Vail-CW/vail-summit/src/settings/settings_cw.h

/*
 * CW Settings Module
 * Handles morse code speed, tone, and key type settings
 */

#ifndef SETTINGS_CW_H
#define SETTINGS_CW_H

#include <Preferences.h>
#include "../core/config.h"

// Key types
enum KeyType {
  KEY_STRAIGHT = 0,
  KEY_IAMBIC_A = 1,
  KEY_IAMBIC_B = 2,
  KEY_ULTIMATIC = 3
};

// CW settings state
enum CWSettingsState {
  CW_SETTING_SPEED,
  CW_SETTING_TONE,
  CW_SETTING_KEY_TYPE
};

// CW settings globals
CWSettingsState cwSettingState = CW_SETTING_SPEED;
int cwSpeed = DEFAULT_WPM;         // WPM
int cwTone = TONE_SIDETONE;        // Hz
KeyType cwKeyType = KEY_IAMBIC_B;  // Default to Iambic B
Preferences cwPrefs;

// Setting selection
int cwSettingSelection = 0;
#define CW_SETTINGS_COUNT 3

// LVGL mode flag - when true, skip legacy draw functions (LVGL handles display)
bool cwSettingsUseLVGL = true;  // Default to LVGL mode

// Forward declarations
void startCWSettings(LGFX &display);
void drawCWSettingsUI(LGFX &display);
int handleCWSettingsInput(char key, LGFX &display);
void saveCWSettings();
void loadCWSettings();

// Load CW settings from flash
void loadCWSettings() {
  if (!cwPrefs.begin("cw", true)) {
    // Namespace missing (fresh device) or NVS unhealthy - keep defaults
    Serial.println("[CW] WARNING: could not open 'cw' namespace read-only, using defaults");
  }
  cwSpeed = cwPrefs.getInt("speed", DEFAULT_WPM);
  cwTone = cwPrefs.getInt("tone", TONE_SIDETONE);
  cwKeyType = (KeyType)cwPrefs.getInt("keytype", KEY_IAMBIC_B);
  cwPrefs.end();

  // Validate settings
  if (cwSpeed < WPM_MIN) cwSpeed = WPM_MIN;
  if (cwSpeed > WPM_MAX) cwSpeed = WPM_MAX;
  if (cwTone < 400) cwTone = 400;
  if (cwTone > 1200) cwTone = 1200;

  Serial.print("CW Settings loaded: ");
  Serial.print(cwSpeed);
  Serial.print(" WPM, ");
  Serial.print(cwTone);
  Serial.print(" Hz, Key type: ");
  Serial.println(cwKeyType);
}

// Save CW settings to flash
void saveCWSettings() {
  if (!cwPrefs.begin("cw", false)) {
    Serial.println("[CW] ERROR: cannot open 'cw' namespace for write - settings NOT saved");
    return;
  }
  // putInt returns bytes written (0 = failure, e.g. NVS partition full)
  bool ok = true;
  ok &= cwPrefs.putInt("speed", cwSpeed) > 0;
  ok &= cwPrefs.putInt("tone", cwTone) > 0;
  ok &= cwPrefs.putInt("keytype", (int)cwKeyType) > 0;
  cwPrefs.end();

  if (ok) {
    Serial.println("CW Settings saved");
  } else {
    Serial.println("[CW] ERROR: NVS write failed (partition full or corrupt?) - settings NOT saved");
  }
}

// Start CW settings mode
void startCWSettings(LGFX &display) {
  cwSettingSelection = 0;
  drawCWSettingsUI(display);
}

// Draw CW settings UI
void drawCWSettingsUI(LGFX &display) {
  if (cwSettingsUseLVGL) return;  // LVGL handles display
  // Clear screen (preserve header)
  display.fillRect(0, HEADER_HEIGHT + 2, SCREEN_WIDTH, SCREEN_HEIGHT - HEADER_HEIGHT - 2, COLOR_BACKGROUND);

  // Clean container card
  int cardX = 20;
  int cardY = 60;
  int cardW = SCREEN_WIDTH - 40;
  int cardH = 150;

  // Solid card background
  display.fillRoundRect(cardX, cardY, cardW, cardH, 10, COLOR_BG_LAYER2);

  // Subtle border
  display.drawRoundRect(cardX, cardY, cardW, cardH, 10, COLOR_BORDER_SUBTLE);

  // Setting 0: Speed (WPM)
  int yPos = cardY + 15;
  bool isSelected = (cwSettingSelection == 0);

  if (isSelected) {
    // Clean selection highlight
    display.fillRoundRect(cardX + 8, yPos, cardW - 16, 36, 8, COLOR_CARD_CYAN);
    display.drawRoundRect(cardX + 8, yPos, cardW - 16, 36, 8, COLOR_BORDER_ACCENT);
  }

  display.setTextSize(1);
  display.setTextColor(isSelected ? COLOR_TEXT_PRIMARY : COLOR_TEXT_SECONDARY);
  display.setCursor(cardX + 15, yPos + 8);
  display.print("Speed");

  display.setTextSize(2);
  display.setTextColor(isSelected ? COLOR_ACCENT_CYAN : COLOR_TEXT_SECONDARY);
  display.setCursor(cardX + 15, yPos + 20);
  display.print(cwSpeed);
  display.print(" WPM");

  // Setting 1: Tone (Hz)
  yPos += 45;
  isSelected = (cwSettingSelection == 1);

  if (isSelected) {
    // Clean selection highlight
    display.fillRoundRect(cardX + 8, yPos, cardW - 16, 36, 8, COLOR_CARD_CYAN);
    display.drawRoundRect(cardX + 8, yPos, cardW - 16, 36, 8, COLOR_BORDER_ACCENT);
  }

  display.setTextSize(1);
  display.setTextColor(isSelected ? COLOR_TEXT_PRIMARY : COLOR_TEXT_SECONDARY);
  display.setCursor(cardX + 15, yPos + 8);
  display.print("Tone");

  display.setTextSize(2);
  display.setTextColor(isSelected ? COLOR_ACCENT_CYAN : COLOR_TEXT_SECONDARY);
  display.setCursor(cardX + 15, yPos + 20);
  display.print(cwTone);
  display.print(" Hz");

  // Setting 2: Key Type
  yPos += 45;
  isSelected = (cwSettingSelection == 2);

  if (isSelected) {
    // Clean selection highlight
    display.fillRoundRect(cardX + 8, yPos, cardW - 16, 36, 8, COLOR_CARD_CYAN);
    display.drawRoundRect(cardX + 8, yPos, cardW - 16, 36, 8, COLOR_BORDER_ACCENT);
  }

  display.setTextSize(1);
  display.setTextColor(isSelected ? COLOR_TEXT_PRIMARY : COLOR_TEXT_SECONDARY);
  display.setCursor(cardX + 15, yPos + 8);
  display.print("Key Type");

  display.setTextSize(2);
  display.setTextColor(isSelected ? COLOR_ACCENT_CYAN : COLOR_TEXT_SECONDARY);
  display.setCursor(cardX + 15, yPos + 20);
  if (cwKeyType == KEY_STRAIGHT) {
    display.print("Straight");
  } else if (cwKeyType == KEY_IAMBIC_A) {
    display.print("Iambic A");
  } else if (cwKeyType == KEY_IAMBIC_B) {
    display.print("Iambic B");
  } else {
    display.print("Ultimatic");
  }

  // Draw footer instructions
  display.setTextSize(1);
  display.setTextColor(COLOR_WARNING);
  String footerText = "\x18\x19 Select  \x1B\x1A Adjust  ESC Back";

  int16_t x1, y1;
  uint16_t w, h;
  getTextBounds_compat(display, footerText.c_str(), 0, 0, &x1, &y1, &w, &h);
  int centerX = (SCREEN_WIDTH - w) / 2;
  display.setCursor(centerX, SCREEN_HEIGHT - 12);
  display.print(footerText);
}

// Handle CW settings input
int handleCWSettingsInput(char key, LGFX &display) {
  bool changed = false;

  if (key == KEY_UP) {
    if (cwSettingSelection > 0) {
      cwSettingSelection--;
      beep(TONE_MENU_NAV, BEEP_SHORT);
      drawCWSettingsUI(display);
    }
    return 1;
  }
  else if (key == KEY_DOWN) {
    if (cwSettingSelection < CW_SETTINGS_COUNT - 1) {
      cwSettingSelection++;
      beep(TONE_MENU_NAV, BEEP_SHORT);
      drawCWSettingsUI(display);
    }
    return 1;
  }
  else if (key == KEY_LEFT) {
    // Decrease value
    if (cwSettingSelection == 0) {
      // Speed
      if (cwSpeed > WPM_MIN) {
        cwSpeed--;
        changed = true;
      }
    } else if (cwSettingSelection == 1) {
      // Tone
      if (cwTone > 400) {
        cwTone -= 50;
        changed = true;
      }
    } else if (cwSettingSelection == 2) {
      // Key type (cycle backward: Ultimatic -> Iambic B -> Iambic A -> Straight)
      if (cwKeyType == KEY_ULTIMATIC) {
        cwKeyType = KEY_IAMBIC_B;
        changed = true;
      } else if (cwKeyType == KEY_IAMBIC_B) {
        cwKeyType = KEY_IAMBIC_A;
        changed = true;
      } else if (cwKeyType == KEY_IAMBIC_A) {
        cwKeyType = KEY_STRAIGHT;
        changed = true;
      }
    }

    if (changed) {
      // Play tone preview if we're adjusting tone setting
      if (cwSettingSelection == 1) {
        beep(cwTone, 150);  // Play the new tone
      } else {
        beep(TONE_MENU_NAV, BEEP_SHORT);
      }
      saveCWSettings();
      drawCWSettingsUI(display);
    }
    return 1;
  }
  else if (key == KEY_RIGHT) {
    // Increase value
    if (cwSettingSelection == 0) {
      // Speed
      if (cwSpeed < WPM_MAX) {
        cwSpeed++;
        changed = true;
      }
    } else if (cwSettingSelection == 1) {
      // Tone
      if (cwTone < 1200) {
        cwTone += 50;
        changed = true;
      }
    } else if (cwSettingSelection == 2) {
      // Key type (cycle forward: Straight -> Iambic A -> Iambic B -> Ultimatic)
      if (cwKeyType == KEY_STRAIGHT) {
        cwKeyType = KEY_IAMBIC_A;
        changed = true;
      } else if (cwKeyType == KEY_IAMBIC_A) {
        cwKeyType = KEY_IAMBIC_B;
        changed = true;
      } else if (cwKeyType == KEY_IAMBIC_B) {
        cwKeyType = KEY_ULTIMATIC;
        changed = true;
      }
    }

    if (changed) {
      // Play tone preview if we're adjusting tone setting
      if (cwSettingSelection == 1) {
        beep(cwTone, 150);  // Play the new tone
      } else {
        beep(TONE_MENU_NAV, BEEP_SHORT);
      }
      saveCWSettings();
      drawCWSettingsUI(display);
    }
    return 1;
  }
  else if (key == KEY_ESC) {
    return -1;  // Exit CW settings
  }

  return 0;
}

#endif // SETTINGS_CW_H
