Vail-CW/vail-summit/src/training/training_practice.h

/*
 * Practice Oscillator Mode
 * Allows free-form morse code practice with paddle/key
 * Includes real-time morse decoding with adaptive speed tracking
 */

#ifndef TRAINING_PRACTICE_H
#define TRAINING_PRACTICE_H

#include "../core/config.h"
#include "../settings/settings_cw.h"
#include "../settings/settings_decoder.h"
#include "../audio/morse_decoder_adaptive.h"
#include "../audio/morse_decoder_direct.h"
#include "../audio/effective_wpm.h"
#include "../keyer/keyer.h"
#include <esp_timer.h>


// Practice mode state
bool practiceActive = false;
bool ditPressed = false;
bool dahPressed = false;
bool lastDitPressed = false;
bool lastDahPressed = false;
unsigned long practiceStartupTime = 0;  // Track startup time for input delay

// Deferred save state - debounces rapid setting changes when holding keys
unsigned long lastSettingSaveTime = 0;
bool settingSavePending = false;
#define SETTING_SAVE_DEBOUNCE_MS 500  // Save 500ms after last change

// Unified keyer instance
static StraightKeyer* practiceKeyer = nullptr;
int ditDuration = 0;

// Statistics
unsigned long practiceStartTime = 0;

// Decoder state - pointer selects Adaptive or Direct at runtime
static MorseDecoder* practiceDecoder = nullptr;

// Timer for direct decoder tick (only used when DECODER_DIRECT is active)
static esp_timer_handle_t decoderTickTimer = nullptr;
static volatile bool decoderTickPending = false;

static void decoderTickCallback(void*) {
  decoderTickPending = true;
}
String decodedText = "";
String decodedMorse = "";
bool showDecoding = true;
bool needsUIUpdate = false;

// Timing capture for decoder
unsigned long lastStateChangeTime = 0;
bool lastToneState = false;
unsigned long lastElementTime = 0;  // Track last element for timeout flush

// "Actual" (effective) WPM tracking - shared measurement (see effective_wpm.h),
// PARIS convention (5 chars = 1 word). Unlike the keyer speed setting, this
// reflects real throughput including any inter-character/word spacing the
// operator adds. Also used by Morse Notes recording so both readouts agree.
static EffectiveWpm practiceEffWpm;

// Forward declarations
void startPracticeMode(LGFX &display);
void updatePracticeOscillator();
void practiceKeyerCallback(bool txOn, int element);
float practiceGetActualWPM();

// LVGL-callable action functions
void practiceHandleEsc();
void practiceHandleClear();
void practiceAdjustSpeed(int delta);
void practiceCycleKeyType(int direction);
void practiceToggleDecoding();
void practiceCheckDeferredSave();

// Start practice mode
void startPracticeMode(LGFX &display) {
  practiceActive = true;
  ditPressed = false;
  dahPressed = false;
  practiceStartupTime = millis();  // Record startup time for input delay

  // Clear any lingering touch sensor state
  touchRead(TOUCH_DIT_PIN);
  touchRead(TOUCH_DAH_PIN);
  delay(50);

  // Reinitialize I2S to ensure clean state
  Serial.println("Reinitializing I2S for practice mode...");
  i2s_zero_dma_buffer(I2S_NUM_0);
  delay(50);

  // Calculate dit duration from current speed setting
  ditDuration = DIT_DURATION(cwSpeed);

  // Initialize unified keyer
  practiceKeyer = getKeyer(cwKeyType);
  practiceKeyer->reset();
  practiceKeyer->setDitDuration(ditDuration);
  practiceKeyer->setTxCallback(practiceKeyerCallback);

  // Reset statistics
  practiceStartTime = millis();

  // Stop any existing tick timer
  if (decoderTickTimer != nullptr) {
    esp_timer_stop(decoderTickTimer);
    esp_timer_delete(decoderTickTimer);
    decoderTickTimer = nullptr;
  }
  decoderTickPending = false;

  // Instantiate the selected decoder
  delete practiceDecoder;
  if (decoderType == DECODER_DIRECT) {
    practiceDecoder = new MorseDecoderDirect(cwSpeed, cwSpeed, 30);
    // Start 5ms periodic timer to drive direct decoder tick
    esp_timer_create_args_t timerArgs = {};
    timerArgs.callback = decoderTickCallback;
    timerArgs.name = "decoder_tick";
    esp_timer_create(&timerArgs, &decoderTickTimer);
    esp_timer_start_periodic(decoderTickTimer, 5000);  // 5000 µs = 5ms
  } else {
    practiceDecoder = new MorseDecoderAdaptive(cwSpeed, cwSpeed, 30);
  }
  practiceDecoder->reset();
  practiceDecoder->flush();
  practiceDecoder->setWPM(cwSpeed);
  decodedText = "";
  decodedMorse = "";
  lastStateChangeTime = 0;  // Don't initialize until first key press
  lastToneState = false;
  lastElementTime = 0;  // Reset element timeout tracker
  showDecoding = true;
  needsUIUpdate = false;
  practiceEffWpm.reset();

  // Setup decoder callbacks
  practiceDecoder->messageCallback = [](String morse, String text) {
    // Process each character in the decoded text individually
    for (int i = 0; i < text.length(); i++) {
      decodedText += text[i];
      // Feed the shared effective-WPM tracker (excludes word-space markers).
      // Counted here (not via decodedText.length()) because the display auto-
      // clears decodedText after 4 lines, which would otherwise reset the count.
      practiceEffWpm.onChar(text[i]);
    }

    // Also track morse pattern
    if (decodedMorse.length() + morse.length() > 100) {
      decodedMorse = "";  // Clear morse if it gets too long
    }
    decodedMorse += morse;

    needsUIUpdate = true;
    // No per-character Serial here: this runs in the keying path, and a
    // print into a full USB CDC buffer can stall the keyer.
  };

  practiceDecoder->speedCallback = [](float wpm, float fwpm) {
    // Fires on every element - no Serial (keying path, see above)
  };

  Serial.println("Practice mode started with decoding enabled");
  Serial.print("Speed: ");
  Serial.print(cwSpeed);
  Serial.print(" WPM, Tone: ");
  Serial.print(cwTone);
  Serial.print(" Hz, Key type: ");
  if (cwKeyType == KEY_STRAIGHT) {
    Serial.println("Straight");
  } else if (cwKeyType == KEY_IAMBIC_A) {
    Serial.println("Iambic A");
  } else if (cwKeyType == KEY_IAMBIC_B) {
    Serial.println("Iambic B");
  } else {
    Serial.println("Ultimatic");
  }
}


// Keyer callback - called by unified keyer when tone state changes
void practiceKeyerCallback(bool txOn, int element) {
  unsigned long currentTime = millis();

  if (txOn) {
    // Tone starting
    if (showDecoding && lastToneState == false) {
      // Send silence duration to decoder (negative). This may flush the
      // previous character (via addTiming's internal word-gap handling),
      // so the effective-WPM burst boundary below must be evaluated AFTER
      // this call, to credit that flushed char to the burst it belongs to.
      if (lastStateChangeTime > 0) {
        float silenceDuration = currentTime - lastStateChangeTime;
        if (silenceDuration > 0) {
          practiceDecoder->addTiming(-silenceDuration);
        }
      }
      lastStateChangeTime = currentTime;
      lastToneState = true;
    }
    practiceEffWpm.onToneStart(currentTime);
    startTone(cwTone);
  } else {
    // Tone stopping
    if (showDecoding && lastToneState == true) {
      // Send tone duration to decoder (positive)
      float toneDuration = currentTime - lastStateChangeTime;
      if (toneDuration > 0) {
        practiceDecoder->addTiming(toneDuration);
        lastElementTime = currentTime;  // Update timeout tracker
      }
      lastStateChangeTime = currentTime;
      lastToneState = false;
    }
    practiceEffWpm.onToneEnd(currentTime);
    stopTone();
  }
}

// Update practice oscillator (called in main loop)
void updatePracticeOscillator() {
  if (!practiceActive) return;
  if (!practiceKeyer) return;

  // Check for deferred settings save
  practiceCheckDeferredSave();

  // Ignore all input for first 1000ms to prevent startup glitches
  if (millis() - practiceStartupTime < 1000) {
    return;
  }

  // Service direct decoder tick (fires every 5ms via esp_timer)
  if (decoderTickPending) {
    decoderTickPending = false;
    if (showDecoding) practiceDecoder->tick();
  }

  // Flush buffered data after word gap silence
  if (showDecoding && lastElementTime > 0 && !ditPressed && !dahPressed) {
    unsigned long timeSinceLastElement = millis() - lastElementTime;
    float wordGapDuration = MorseWPM::wordGap(practiceDecoder->getWPM());
    if (timeSinceLastElement > wordGapDuration) {
      practiceDecoder->flush();
      lastElementTime = 0;
    }
  }

  // Get paddle state from centralized handler (includes debounce)
  bool newDitPressed, newDahPressed;
  getPaddleState(&newDitPressed, &newDahPressed);

  // Feed paddle state to unified keyer
  if (newDitPressed != ditPressed) {
    practiceKeyer->key(PADDLE_DIT, newDitPressed);
    ditPressed = newDitPressed;
  }
  if (newDahPressed != dahPressed) {
    practiceKeyer->key(PADDLE_DAH, newDahPressed);
    dahPressed = newDahPressed;
  }

  // Tick the keyer state machine
  practiceKeyer->tick(millis());

  // Keep tone playing if keyer is active (for audio buffer continuity)
  if (practiceKeyer->isTxActive()) {
    continueTone(cwTone);
  }

  // Update visual feedback if state changed
  if (ditPressed != lastDitPressed || dahPressed != lastDahPressed) {
    lastDitPressed = ditPressed;
    lastDahPressed = dahPressed;
  }
}

// ============================================
// LVGL-Callable Action Functions
// ============================================

// Handle ESC key - stop practice and prepare for exit
void practiceHandleEsc() {
  practiceActive = false;
  stopTone();
  if (decoderTickTimer != nullptr) {
    esp_timer_stop(decoderTickTimer);
    esp_timer_delete(decoderTickTimer);
    decoderTickTimer = nullptr;
  }
  decoderTickPending = false;
  if (practiceKeyer) {
    practiceKeyer->reset();
  }
  practiceDecoder->flush();  // Decode any remaining buffered timings
  practiceEffWpm.reset();

  // Save any pending settings before exit
  if (settingSavePending) {
    markDeferredSave(saveCWSettings);
    settingSavePending = false;
    Serial.println("[Practice] Saved pending settings on exit");
  }

  Serial.println("[Practice] ESC - exiting practice mode");
}

// Clear decoder text
void practiceHandleClear() {
  decodedText = "";
  decodedMorse = "";
  practiceDecoder->reset();
  practiceDecoder->flush();
  practiceEffWpm.reset();
  needsUIUpdate = true;  // Signal LVGL to update display
  beep(TONE_MENU_NAV, BEEP_SHORT);
  Serial.println("[Practice] Cleared decoder text");
}

// Adjust WPM speed (delta can be any value, e.g., 1, 2, 4 based on acceleration)
void practiceAdjustSpeed(int delta) {
  int newSpeed = cwSpeed + delta;
  if (newSpeed >= WPM_MIN && newSpeed <= WPM_MAX) {
    cwSpeed = newSpeed;
    ditDuration = DIT_DURATION(cwSpeed);
    practiceDecoder->setWPM(cwSpeed);
    if (practiceKeyer) {
      practiceKeyer->setDitDuration(ditDuration);
    }

    // Mark save as pending instead of immediate save (debounces rapid changes)
    settingSavePending = true;
    lastSettingSaveTime = millis();

    beep(TONE_MENU_NAV, BEEP_SHORT);
    Serial.printf("[Practice] Speed changed to %d WPM (save pending)\n", cwSpeed);
  }
}

// Check and perform deferred save of CW settings
// Call this from updatePracticeOscillator() to save after debounce period
void practiceCheckDeferredSave() {
  if (settingSavePending && (millis() - lastSettingSaveTime > SETTING_SAVE_DEBOUNCE_MS)) {
    markDeferredSave(saveCWSettings);
    settingSavePending = false;
    Serial.println("[Practice] Deferred CW settings save completed");
  }
}

// Cycle key type (+1 forward, -1 backward)
void practiceCycleKeyType(int direction) {
  if (direction > 0) {
    // Cycle forward: Straight -> Iambic A -> Iambic B -> Ultimatic -> Straight
    if (cwKeyType == KEY_STRAIGHT) {
      cwKeyType = KEY_IAMBIC_A;
    } else if (cwKeyType == KEY_IAMBIC_A) {
      cwKeyType = KEY_IAMBIC_B;
    } else if (cwKeyType == KEY_IAMBIC_B) {
      cwKeyType = KEY_ULTIMATIC;
    } else {
      cwKeyType = KEY_STRAIGHT;
    }
  } else {
    // Cycle backward: Ultimatic -> Iambic B -> Iambic A -> Straight -> Ultimatic
    if (cwKeyType == KEY_ULTIMATIC) {
      cwKeyType = KEY_IAMBIC_B;
    } else if (cwKeyType == KEY_IAMBIC_B) {
      cwKeyType = KEY_IAMBIC_A;
    } else if (cwKeyType == KEY_IAMBIC_A) {
      cwKeyType = KEY_STRAIGHT;
    } else {
      cwKeyType = KEY_ULTIMATIC;
    }
  }

  // Reinitialize keyer with new type
  practiceKeyer = getKeyer(cwKeyType);
  practiceKeyer->reset();
  practiceKeyer->setDitDuration(ditDuration);
  practiceKeyer->setTxCallback(practiceKeyerCallback);

  // Mark save as pending (use same debounce as speed changes)
  settingSavePending = true;
  lastSettingSaveTime = millis();

  beep(TONE_MENU_NAV, BEEP_SHORT);

  const char* keyTypeStr = (cwKeyType == KEY_STRAIGHT) ? "Straight" :
                           (cwKeyType == KEY_IAMBIC_A) ? "Iambic A" :
                           (cwKeyType == KEY_IAMBIC_B) ? "Iambic B" : "Ultimatic";
  Serial.printf("[Practice] Key type changed to %s (save pending)\n", keyTypeStr);
}

// Toggle decoding display
void practiceToggleDecoding() {
  showDecoding = !showDecoding;
  beep(TONE_MENU_NAV, BEEP_SHORT);
  Serial.printf("[Practice] Decoding %s\n", showDecoding ? "enabled" : "disabled");
}

// Get the current "actual" (effective) WPM reading for the CW Practice
// screen - the current sending burst only (responsive; freezes at its last
// value during a pause; -1 until there's a valid reading).
float practiceGetActualWPM() {
  return practiceEffWpm.burstWpm();
}

#endif // TRAINING_PRACTICE_H
