Vail-CW/vail-summit/src/core/task_manager.h

/*
 * VAIL SUMMIT - FreeRTOS Task Manager
 * Dual-core task management for ESP32-S3
 *
 * Core 0: Audio Task (high priority) - I2S generation, morse tones, decoder timing
 * Core 1: UI Task (Arduino loop) - LVGL rendering, input handling, network
 */

#ifndef TASK_MANAGER_H
#define TASK_MANAGER_H

#include <freertos/FreeRTOS.h>
#include <freertos/task.h>
#include <freertos/queue.h>
#include <freertos/semphr.h>
#include "config.h"
#include "morse_code.h"

// ============================================
// Task Configuration
// ============================================

#define AUDIO_TASK_STACK_SIZE   8192    // Stack size for audio task
#define AUDIO_TASK_PRIORITY     (configMAX_PRIORITIES - 1)  // Highest priority
// Run audio on Core 0. Core 1 (the Arduino/LVGL loop + display SPI-DMA) caused
// CONSTANT distortion - the audio task fights the display renderer continuously.
// Core 0 is clean in steady state; its only artifact is a brief (~10s) startup
// distortion while the WiFi stack (also Core 0) is connecting, which the larger
// I2S DMA buffer (see i2s_audio.h) is meant to ride out.
#define AUDIO_TASK_CORE         0

// ============================================
// Task Handles
// ============================================

static TaskHandle_t audioTaskHandle = NULL;

// ============================================
// Thread-Safe Audio Request Structure
// ============================================

// Tone request types
enum ToneRequestType {
    TONE_REQ_NONE = 0,
    TONE_REQ_PLAY,          // Play a tone for specific duration
    TONE_REQ_START,         // Start continuous tone
    TONE_REQ_CONTINUE,      // Continue current tone (fill buffer)
    TONE_REQ_STOP           // Stop current tone
};

// Thread-safe tone request (written by UI core, read by audio core)
struct ToneRequest {
    volatile ToneRequestType type;
    volatile int frequency;
    volatile int duration_ms;
};

static volatile ToneRequest toneRequest = {TONE_REQ_NONE, 0, 0};

// Audio state (managed by audio task, read by UI for status)
static volatile bool audioTaskRunning = false;
static volatile bool toneCurrentlyPlaying = false;
static volatile int currentToneFrequency = 0;

// Mutex for protecting shared state
static SemaphoreHandle_t audioMutex = NULL;

// ============================================
// Decoded Character Queue
// ============================================

// Queue for decoded characters (audio core produces, UI core consumes)
#define DECODED_CHAR_QUEUE_SIZE 32
static QueueHandle_t decodedCharQueue = NULL;

// ============================================
// Paddle Input State (sampled by audio task)
// ============================================

struct PaddleState {
    volatile bool ditPressed;
    volatile bool dahPressed;
    volatile unsigned long ditPressTime;
    volatile unsigned long dahPressTime;
    // Debounce state
    volatile bool ditRaw;
    volatile bool dahRaw;
    volatile unsigned long ditLastChange;
    volatile unsigned long dahLastChange;
};

static volatile PaddleState paddleState = {false, false, 0, 0, false, false, 0, 0};

// ============================================
// Core 0 Paddle Callback Support
// ============================================
// Allows modes to register a callback for paddle sampling on Core 0
// This provides precise ~1ms timing for keyer logic

// Paddle callback function type
// Called from Core 0 audio task with current paddle state and millis()
typedef void (*PaddleCallbackFn)(bool ditPressed, bool dahPressed, unsigned long now);

// Registered paddle callback (set by modes that need Core 0 timing)
static volatile PaddleCallbackFn paddleCallback = nullptr;

/*
 * Register a paddle callback to be called from Core 0
 * Set to nullptr to disable
 */
void registerPaddleCallback(PaddleCallbackFn callback) {
    paddleCallback = callback;
}

/*
 * Check if paddle callback is registered
 */
bool hasPaddleCallback() {
    return paddleCallback != nullptr;
}

// ============================================
// Async Morse String Playback
// ============================================

#define MORSE_PLAYBACK_MAX_LENGTH 128  // Max string length for async playback

// Morse playback state machine
enum MorsePlaybackState {
    MORSE_IDLE = 0,           // No playback active
    MORSE_PLAYING_ELEMENT,    // Playing a dit or dah
    MORSE_ELEMENT_GAP,        // Gap between dits/dahs in same letter
    MORSE_LETTER_GAP,         // Gap between letters
    MORSE_WORD_GAP,           // Gap between words
    MORSE_COMPLETE            // Playback finished
};

// Morse playback request structure
struct MorsePlaybackRequest {
    volatile bool active;           // Playback in progress
    volatile bool cancelled;        // Cancellation requested
    char text[MORSE_PLAYBACK_MAX_LENGTH];  // Text to play
    volatile int textLength;        // Length of text
    volatile int wpm;               // Words per minute (character speed)
    volatile int effectiveWPM;      // Effective WPM for Farnsworth (spacing speed)
    volatile bool useFarnsworth;    // Use Farnsworth timing (different element vs spacing speed)
    volatile int toneHz;            // Tone frequency
    volatile int charIndex;         // Current character in text
    volatile int elementIndex;      // Current element in character pattern
    volatile MorsePlaybackState state;  // Current state
    volatile unsigned long stateEndTime;  // When current state ends
    volatile bool complete;         // Playback finished flag
};

static volatile MorsePlaybackRequest morsePlayback = {
    false, false, "", 0, 0, 0, false, 0, 0, 0, MORSE_IDLE, 0, false
};

// Uses morseTable[] and getMorseCode() from morse_code.h (no duplicate table needed)

// ============================================
// Thread-Safe API Functions (called from UI core)
// ============================================

/*
 * Request a tone to be played
 * Non-blocking - sets request flags for audio task
 */
void requestPlayTone(int frequency, int duration_ms) {
    if (xSemaphoreTake(audioMutex, pdMS_TO_TICKS(10)) == pdTRUE) {
        toneRequest.frequency = frequency;
        toneRequest.duration_ms = duration_ms;
        toneRequest.type = TONE_REQ_PLAY;
        xSemaphoreGive(audioMutex);
    }
}

/*
 * Request to start a continuous tone
 */
void requestStartTone(int frequency) {
    if (xSemaphoreTake(audioMutex, pdMS_TO_TICKS(10)) == pdTRUE) {
        toneRequest.frequency = frequency;
        toneRequest.duration_ms = 0;
        toneRequest.type = TONE_REQ_START;
        xSemaphoreGive(audioMutex);
    }
}

/*
 * Request to stop the current tone
 */
void requestStopTone() {
    if (xSemaphoreTake(audioMutex, pdMS_TO_TICKS(10)) == pdTRUE) {
        toneRequest.type = TONE_REQ_STOP;
        xSemaphoreGive(audioMutex);
    }
}

/*
 * Request a beep (blocking on UI side - waits for completion)
 */
void requestBeep(int frequency, int duration_ms) {
    requestPlayTone(frequency, duration_ms);
    // Wait for tone to complete (approximate)
    vTaskDelay(pdMS_TO_TICKS(duration_ms + 20));
}

/*
 * Check if a tone is currently playing
 */
bool isAudioTonePlaying() {
    return toneCurrentlyPlaying;
}

/*
 * Get a decoded character from the queue (non-blocking)
 * Returns 0 if queue is empty
 */
char getDecodedChar() {
    char c = 0;
    if (decodedCharQueue != NULL) {
        xQueueReceive(decodedCharQueue, &c, 0);
    }
    return c;
}

/*
 * Check if there are decoded characters available
 */
bool hasDecodedChars() {
    if (decodedCharQueue == NULL) return false;
    return uxQueueMessagesWaiting(decodedCharQueue) > 0;
}

// ============================================
// Async Morse String Playback API (called from UI core)
// ============================================

/*
 * Request to play a morse string asynchronously
 * Non-blocking - returns immediately, audio task handles playback
 */
void requestPlayMorseString(const char* str, int wpm, int toneHz = TONE_SIDETONE) {
    if (str == nullptr || strlen(str) == 0) return;

    if (xSemaphoreTake(audioMutex, pdMS_TO_TICKS(20)) == pdTRUE) {
        // Stop any current playback
        morsePlayback.cancelled = true;

        // Wait a moment for audio task to see cancellation
        xSemaphoreGive(audioMutex);
        vTaskDelay(pdMS_TO_TICKS(10));

        // Now set up new playback
        if (xSemaphoreTake(audioMutex, pdMS_TO_TICKS(20)) == pdTRUE) {
            // Copy text (safely)
            int len = strlen(str);
            if (len > MORSE_PLAYBACK_MAX_LENGTH - 1) {
                len = MORSE_PLAYBACK_MAX_LENGTH - 1;
            }
            strncpy((char*)morsePlayback.text, str, len);
            ((char*)morsePlayback.text)[len] = '\0';

            morsePlayback.textLength = len;
            morsePlayback.wpm = wpm;
            morsePlayback.effectiveWPM = wpm;  // No Farnsworth - same as wpm
            morsePlayback.useFarnsworth = false;
            morsePlayback.toneHz = toneHz;
            morsePlayback.charIndex = 0;
            morsePlayback.elementIndex = 0;
            morsePlayback.state = MORSE_IDLE;  // Will start on next audio task cycle
            morsePlayback.stateEndTime = 0;
            morsePlayback.complete = false;
            morsePlayback.cancelled = false;
            morsePlayback.active = true;

            Serial.printf("[MorsePlayback] Started: '%s' @ %d WPM, %d Hz\n", str, wpm, toneHz);
            xSemaphoreGive(audioMutex);
        }
    }
}

/*
 * Request to play a morse string with Farnsworth timing asynchronously
 * characterWPM: speed for dits/dahs within a character (typically 25 WPM)
 * effectiveWPM: overall speed, determines inter-character/word spacing (typically 6-11 WPM)
 * Non-blocking - returns immediately, audio task handles playback
 */
void requestPlayMorseStringFarnsworth(const char* str, int characterWPM, int effectiveWPM, int toneHz = TONE_SIDETONE) {
    if (str == nullptr || strlen(str) == 0) return;

    if (xSemaphoreTake(audioMutex, pdMS_TO_TICKS(20)) == pdTRUE) {
        // Stop any current playback
        morsePlayback.cancelled = true;

        // Wait a moment for audio task to see cancellation
        xSemaphoreGive(audioMutex);
        vTaskDelay(pdMS_TO_TICKS(10));

        // Now set up new playback
        if (xSemaphoreTake(audioMutex, pdMS_TO_TICKS(20)) == pdTRUE) {
            // Copy text (safely)
            int len = strlen(str);
            if (len > MORSE_PLAYBACK_MAX_LENGTH - 1) {
                len = MORSE_PLAYBACK_MAX_LENGTH - 1;
            }
            strncpy((char*)morsePlayback.text, str, len);
            ((char*)morsePlayback.text)[len] = '\0';

            morsePlayback.textLength = len;
            morsePlayback.wpm = characterWPM;           // Character element speed
            morsePlayback.effectiveWPM = effectiveWPM;  // Spacing speed
            morsePlayback.useFarnsworth = (characterWPM != effectiveWPM);
            morsePlayback.toneHz = toneHz;
            morsePlayback.charIndex = 0;
            morsePlayback.elementIndex = 0;
            morsePlayback.state = MORSE_IDLE;  // Will start on next audio task cycle
            morsePlayback.stateEndTime = 0;
            morsePlayback.complete = false;
            morsePlayback.cancelled = false;
            morsePlayback.active = true;

            Serial.printf("[MorsePlayback] Farnsworth started: '%s' @ %d/%d WPM, %d Hz\n",
                          str, characterWPM, effectiveWPM, toneHz);
            xSemaphoreGive(audioMutex);
        }
    }
}

/*
 * Check if morse playback is currently active
 */
bool isMorsePlaybackActive() {
    return morsePlayback.active && !morsePlayback.complete;
}

/*
 * Check if morse playback has completed
 */
bool isMorsePlaybackComplete() {
    return morsePlayback.complete;
}

/*
 * Cancel current morse playback
 */
void cancelMorsePlayback() {
    if (xSemaphoreTake(audioMutex, pdMS_TO_TICKS(10)) == pdTRUE) {
        morsePlayback.cancelled = true;
        xSemaphoreGive(audioMutex);
    }
}

/*
 * Get current playback progress (0.0 to 1.0)
 */
float getMorsePlaybackProgress() {
    if (!morsePlayback.active || morsePlayback.textLength == 0) return 0.0f;
    return (float)morsePlayback.charIndex / (float)morsePlayback.textLength;
}

/*
 * Reset morse playback state (call when entering modes)
 */
void resetMorsePlayback() {
    if (xSemaphoreTake(audioMutex, pdMS_TO_TICKS(10)) == pdTRUE) {
        morsePlayback.active = false;
        morsePlayback.cancelled = false;
        morsePlayback.complete = false;
        morsePlayback.charIndex = 0;
        morsePlayback.elementIndex = 0;
        morsePlayback.state = MORSE_IDLE;
        xSemaphoreGive(audioMutex);
    }
}

// ============================================
// Internal Audio Task Functions
// ============================================

// Forward declarations for i2s_audio.h functions that will be called internally
extern void playToneInternal(int frequency, int duration_ms);
extern void IRAM_ATTR startToneInternal(int frequency);
extern void IRAM_ATTR continueToneInternal(int frequency);
extern void IRAM_ATTR stopToneInternal();
extern bool isTonePlayingInternal();

/*
 * Process audio requests from the queue
 * Called by audio task
 */
void IRAM_ATTR processAudioRequests() {
    ToneRequestType reqType = TONE_REQ_NONE;
    int reqFreq = 0;
    int reqDuration = 0;

    // Get current request with mutex protection
    if (xSemaphoreTake(audioMutex, pdMS_TO_TICKS(5)) == pdTRUE) {
        reqType = toneRequest.type;
        reqFreq = toneRequest.frequency;
        reqDuration = toneRequest.duration_ms;
        toneRequest.type = TONE_REQ_NONE;  // Clear request
        xSemaphoreGive(audioMutex);
    }

    // Process the request
    switch (reqType) {
        case TONE_REQ_PLAY:
            toneCurrentlyPlaying = true;
            currentToneFrequency = reqFreq;
            playToneInternal(reqFreq, reqDuration);
            toneCurrentlyPlaying = false;
            currentToneFrequency = 0;
            break;

        case TONE_REQ_START:
            toneCurrentlyPlaying = true;
            currentToneFrequency = reqFreq;
            startToneInternal(reqFreq);
            break;

        case TONE_REQ_CONTINUE:
            if (toneCurrentlyPlaying) {
                continueToneInternal(currentToneFrequency);
            }
            break;

        case TONE_REQ_STOP:
            stopToneInternal();
            toneCurrentlyPlaying = false;
            currentToneFrequency = 0;
            break;

        default:
            // If tone is playing, keep buffer filled
            if (toneCurrentlyPlaying) {
                continueToneInternal(currentToneFrequency);
            }
            break;
    }
}

/*
 * Sample paddle input and call registered callback
 * Called by audio task for precise timing (~1ms intervals)
 * Includes debounce to prevent double-dits from contact bounce
 */
void IRAM_ATTR samplePaddleInput() {
    // Read raw paddle pins
    bool rawDit = (digitalRead(DIT_PIN) == PADDLE_ACTIVE);
    bool rawDah = (digitalRead(DAH_PIN) == PADDLE_ACTIVE);

    // Read capacitive touch
    if (!rawDit) {
        rawDit = (touchRead(TOUCH_DIT_PIN) > TOUCH_THRESHOLD);
    }
    if (!rawDah) {
        rawDah = (touchRead(TOUCH_DAH_PIN) > TOUCH_THRESHOLD);
    }

    unsigned long now = millis();

    // Debounce dit paddle - only register change after stable for PADDLE_DEBOUNCE_MS
    if (rawDit != paddleState.ditRaw) {
        paddleState.ditLastChange = now;
        paddleState.ditRaw = rawDit;
    }
    bool dit = paddleState.ditPressed;
    if ((now - paddleState.ditLastChange) >= PADDLE_DEBOUNCE_MS) {
        dit = paddleState.ditRaw;
    }

    // Debounce dah paddle
    if (rawDah != paddleState.dahRaw) {
        paddleState.dahLastChange = now;
        paddleState.dahRaw = rawDah;
    }
    bool dah = paddleState.dahPressed;
    if ((now - paddleState.dahLastChange) >= PADDLE_DEBOUNCE_MS) {
        dah = paddleState.dahRaw;
    }

    // Update state with timestamps
    if (dit && !paddleState.ditPressed) {
        paddleState.ditPressTime = now;
    }
    if (dah && !paddleState.dahPressed) {
        paddleState.dahPressTime = now;
    }

    paddleState.ditPressed = dit;
    paddleState.dahPressed = dah;

    // Call registered paddle callback if set (for Core 0 keyer timing)
    if (paddleCallback != nullptr) {
        paddleCallback(dit, dah, now);
    }
}

/*
 * Get current paddle state (called from UI or decoder)
 */
void getPaddleState(bool* dit, bool* dah) {
    *dit = paddleState.ditPressed;
    *dah = paddleState.dahPressed;
}

/*
 * Process morse string playback state machine
 * Called by audio task - runs non-blocking state machine for async playback
 */
void IRAM_ATTR processMorsePlayback() {
    // Skip if no active playback
    if (!morsePlayback.active) return;

    // Check for cancellation
    if (morsePlayback.cancelled) {
        stopToneInternal();
        morsePlayback.active = false;
        morsePlayback.complete = true;
        morsePlayback.cancelled = false;
        // No Serial here - this runs on the IRAM audio hot path and
        // Serial.print* is flash-resident. (Was "[MorsePlayback] Cancelled".)
        return;
    }

    unsigned long now = millis();

    // Calculate timing based on WPM
    // Standard: 1 unit = 1200/WPM ms
    int charUnit = 1200 / morsePlayback.wpm;  // For dits/dahs within character
    int spaceUnit = charUnit;  // Default same as character

    // Farnsworth timing: use slower effective WPM for inter-character/word spacing
    if (morsePlayback.useFarnsworth && morsePlayback.effectiveWPM > 0) {
        spaceUnit = 1200 / morsePlayback.effectiveWPM;
    }

    int ditDuration = charUnit;
    int dahDuration = charUnit * 3;
    int elementGap = charUnit;       // Gap between elements within a character (always use char speed)
    int letterGap = spaceUnit * 3;   // Gap between characters (Farnsworth stretches this)
    int wordGap = spaceUnit * 7;     // Gap between words (Farnsworth stretches this)

    // State machine
    switch (morsePlayback.state) {
        case MORSE_IDLE: {
            // Start playing - find first valid character
            while (morsePlayback.charIndex < morsePlayback.textLength) {
                char c = morsePlayback.text[morsePlayback.charIndex];

                if (c == ' ') {
                    // Word gap - transition to MORSE_WORD_GAP
                    morsePlayback.state = MORSE_WORD_GAP;
                    morsePlayback.stateEndTime = now + (wordGap - letterGap);  // Subtract letter gap already added
                    morsePlayback.charIndex++;
                    return;
                }

                const char* pattern = getMorseCode(c);
                if (pattern != nullptr) {
                    // Valid character - start playing first element
                    morsePlayback.elementIndex = 0;
                    char element = pattern[0];

                    if (element == '.') {
                        startToneInternal(morsePlayback.toneHz);
                        morsePlayback.state = MORSE_PLAYING_ELEMENT;
                        morsePlayback.stateEndTime = now + ditDuration;
                    } else if (element == '-') {
                        startToneInternal(morsePlayback.toneHz);
                        morsePlayback.state = MORSE_PLAYING_ELEMENT;
                        morsePlayback.stateEndTime = now + dahDuration;
                    }
                    return;
                }

                // Unknown character - skip it
                morsePlayback.charIndex++;
            }

            // No more characters - playback complete
            morsePlayback.state = MORSE_COMPLETE;
            morsePlayback.complete = true;
            morsePlayback.active = false;
            // No Serial here - IRAM hot path. (Was "[MorsePlayback] Complete".)
            break;
        }

        case MORSE_PLAYING_ELEMENT: {
            // Keep I2S buffer filled during tone
            continueToneInternal(morsePlayback.toneHz);

            // Check if element duration has elapsed
            if (now >= morsePlayback.stateEndTime) {
                stopToneInternal();

                // Get current character pattern
                char c = morsePlayback.text[morsePlayback.charIndex];
                const char* pattern = getMorseCode(c);

                if (pattern == nullptr) {
                    // Should not happen, but handle gracefully
                    morsePlayback.charIndex++;
                    morsePlayback.state = MORSE_IDLE;
                    return;
                }

                // Move to next element
                morsePlayback.elementIndex++;

                if (pattern[morsePlayback.elementIndex] != '\0') {
                    // More elements in this character - add element gap
                    morsePlayback.state = MORSE_ELEMENT_GAP;
                    morsePlayback.stateEndTime = now + elementGap;
                } else {
                    // Character complete - move to next character
                    morsePlayback.charIndex++;

                    if (morsePlayback.charIndex >= morsePlayback.textLength) {
                        // All done
                        morsePlayback.state = MORSE_COMPLETE;
                        morsePlayback.complete = true;
                        morsePlayback.active = false;
                        // No Serial here - IRAM hot path. (Was "[MorsePlayback] Complete".)
                    } else if (morsePlayback.text[morsePlayback.charIndex] == ' ') {
                        // Next is space - word gap (already have letter gap implicitly)
                        morsePlayback.charIndex++;
                        morsePlayback.state = MORSE_WORD_GAP;
                        morsePlayback.stateEndTime = now + wordGap;
                    } else {
                        // Next is a character - letter gap
                        morsePlayback.state = MORSE_LETTER_GAP;
                        morsePlayback.stateEndTime = now + letterGap;
                    }
                }
            }
            break;
        }

        case MORSE_ELEMENT_GAP: {
            // Wait for element gap to complete
            if (now >= morsePlayback.stateEndTime) {
                // Start next element
                char c = morsePlayback.text[morsePlayback.charIndex];
                const char* pattern = getMorseCode(c);

                if (pattern != nullptr && pattern[morsePlayback.elementIndex] != '\0') {
                    char element = pattern[morsePlayback.elementIndex];

                    if (element == '.') {
                        startToneInternal(morsePlayback.toneHz);
                        morsePlayback.state = MORSE_PLAYING_ELEMENT;
                        morsePlayback.stateEndTime = now + ditDuration;
                    } else if (element == '-') {
                        startToneInternal(morsePlayback.toneHz);
                        morsePlayback.state = MORSE_PLAYING_ELEMENT;
                        morsePlayback.stateEndTime = now + dahDuration;
                    }
                } else {
                    // Pattern ended unexpectedly - move to next char
                    morsePlayback.charIndex++;
                    morsePlayback.state = MORSE_IDLE;
                }
            }
            break;
        }

        case MORSE_LETTER_GAP: {
            // Wait for letter gap to complete
            if (now >= morsePlayback.stateEndTime) {
                // Start next character
                morsePlayback.state = MORSE_IDLE;
            }
            break;
        }

        case MORSE_WORD_GAP: {
            // Wait for word gap to complete
            if (now >= morsePlayback.stateEndTime) {
                // Continue to next character
                morsePlayback.state = MORSE_IDLE;
            }
            break;
        }

        case MORSE_COMPLETE: {
            // Nothing to do - playback finished
            break;
        }
    }
}

// ============================================
// Audio Task
// ============================================

/*
 * Audio task - runs on Core 0
 * High priority, dedicated to audio processing
 */
void IRAM_ATTR audioTask(void* parameter) {
    Serial.println("[AudioTask] Started on Core 0");  // One-time, before the loop - fine.
    audioTaskRunning = true;

    while (true) {
#if AUDIO_PERF_INSTRUMENT
        uint32_t aperf_iter_start = micros();
#endif
        // Process any pending audio requests (single tone API)
        processAudioRequests();

        // Process morse string playback (async playback API)
        processMorsePlayback();

        // Sample paddle input with precise timing
        samplePaddleInput();

#if AUDIO_PERF_INSTRUMENT
        {
            uint32_t dt = micros() - aperf_iter_start;
            aperf_iterations++;
            if (dt > aperf_worst_loop_us) aperf_worst_loop_us = dt;
            if (dt > 5000) aperf_over5ms_count++;
        }
#endif

        // Yield to allow other tasks, but keep loop tight (~1ms)
        vTaskDelay(1);

        // Outside the measured region - this is the only place the once-per-
        // second Serial.printf report is allowed to run.
        reportAudioPerf();
    }
}

// ============================================
// Task Setup
// ============================================

/*
 * Initialize task manager and start audio task on Core 0
 * Call this from setup() after hardware initialization
 */
void setupTaskManager() {
    Serial.println("[TaskManager] Initializing...");

    // Create mutex for audio state protection
    audioMutex = xSemaphoreCreateMutex();
    if (audioMutex == NULL) {
        Serial.println("[TaskManager] ERROR: Failed to create audio mutex!");
        return;
    }

    // Create queue for decoded characters
    decodedCharQueue = xQueueCreate(DECODED_CHAR_QUEUE_SIZE, sizeof(char));
    if (decodedCharQueue == NULL) {
        Serial.println("[TaskManager] ERROR: Failed to create decoded char queue!");
        return;
    }

    // Create audio task pinned to Core 0
    BaseType_t result = xTaskCreatePinnedToCore(
        audioTask,              // Task function
        "AudioTask",            // Task name
        AUDIO_TASK_STACK_SIZE,  // Stack size
        NULL,                   // Parameters
        AUDIO_TASK_PRIORITY,    // Priority
        &audioTaskHandle,       // Task handle
        AUDIO_TASK_CORE         // Core ID
    );

    if (result != pdPASS) {
        Serial.println("[TaskManager] ERROR: Failed to create audio task!");
        return;
    }

    Serial.printf("[TaskManager] Audio task created on Core %d with priority %d\n",
                  AUDIO_TASK_CORE, AUDIO_TASK_PRIORITY);
    Serial.printf("[TaskManager] UI runs on Core %d (Arduino loop)\n", 1);
}

/*
 * Check if audio task is running
 */
bool isAudioTaskRunning() {
    return audioTaskRunning;
}

/*
 * Send a decoded character to the UI queue
 * Called from decoder running on audio task
 */
void sendDecodedChar(char c) {
    if (decodedCharQueue != NULL) {
        xQueueSend(decodedCharQueue, &c, 0);  // Non-blocking
    }
}

#endif // TASK_MANAGER_H
