Vail-CW/vail-summit/src/bluetooth/ble_midi.h

/*
 * BLE MIDI Mode
 * Bidirectional BLE MIDI for Vail repeater and MIDI-enabled morse tools
 * - Sends: Processed keyer output as MIDI Note On/Off
 * - Receives: Sidetone from computer, CC messages for speed/tone/keyer type
 *
 * MIDI Protocol (Vail Adapter Spec):
 * - Outgoing: Note 0 (C) for keyed output, Notes 1/2 for passthrough dit/dah
 * - Incoming CC1: Dit duration (speed), CC2: Sidetone note
 * - Incoming Program Change: Keyer type selection
 */

#ifndef BLE_MIDI_H
#define BLE_MIDI_H

#include <NimBLEDevice.h>
#include "ble_core.h"
#include "ble_keyboard_host.h"
#include "../core/config.h"
#include "../audio/i2s_audio.h"
#include "../settings/settings_cw.h"
#include "../keyer/keyer.h"

// BLE MIDI Service and Characteristic UUIDs (standard BLE MIDI spec)
#define MIDI_SERVICE_UUID        "03b80e5a-ede8-4b33-a751-6ce34ec4c700"
#define MIDI_CHARACTERISTIC_UUID "7772e5db-3868-4112-a1a9-f2669d106bf3"

// MIDI message types
#define MIDI_NOTE_OFF     0x80
#define MIDI_NOTE_ON      0x90
#define MIDI_CONTROL_CHANGE 0xB0
#define MIDI_PROGRAM_CHANGE 0xC0

// MIDI notes (Vail Adapter spec)
#define MIDI_NOTE_STRAIGHT 0   // C - Straight key / keyed output
#define MIDI_NOTE_DIT      1   // C# - Dit (passthrough mode)
#define MIDI_NOTE_DAH      2   // D - Dah (passthrough mode)

// MIDI Control Change numbers
#define MIDI_CC_DIT_DURATION 1  // CC1 - Dit duration in 2ms units
#define MIDI_CC_SIDETONE_NOTE 2 // CC2 - Sidetone MIDI note number

// MIDI Keyer Programs (Vail Adapter spec)
#define MIDI_KEYER_PASSTHROUGH  0
#define MIDI_KEYER_STRAIGHT     1
#define MIDI_KEYER_BUG          2
#define MIDI_KEYER_IAMBIC_A     7
#define MIDI_KEYER_IAMBIC_B     8

// BLE MIDI state
struct BLEMIDIState {
  bool active = false;
  bool isKeying = false;           // Current key state (for output)
  bool lastDitPressed = false;
  bool lastDahPressed = false;

  // MIDI-controlled settings
  int midiDitDuration = 0;         // 0 = use device settings
  int midiSidetoneNote = 69;       // A4 = 440Hz
  int midiKeyerProgram = MIDI_KEYER_IAMBIC_B;  // Default keyer type

  // BLE characteristics
  NimBLEService* midiService = nullptr;
  NimBLECharacteristic* midiCharacteristic = nullptr;

  unsigned long lastUpdateTime = 0;
};

BLEMIDIState btMIDI;

// Unified keyer for BT MIDI
static StraightKeyer* btMIDIKeyer = nullptr;
static bool btMIDIDitPressed = false;
static bool btMIDIDahPressed = false;

// Forward declarations
void startBTMIDI(LGFX& display);
void drawBTMIDIUI(LGFX& display);
int handleBTMIDIInput(char key, LGFX& display);
void updateBTMIDI();
void stopBTMIDI();
void sendMIDINoteOn(uint8_t note, uint8_t velocity);
void sendMIDINoteOff(uint8_t note);
void onMIDIReceived(uint8_t* data, size_t length);
void btMidiKeyerHandler();
void btMidiPassthroughHandler();
void btMidiInitKeyer();
int midiNoteToFrequency(int note);
int getDitDuration();
const char* getBTMIDIKeyerProgramName();

// Forward declarations for LVGL UI updates (defined in lv_mode_screens.h)
extern void updateBTMIDIStatus(const char* status, bool connected);
extern void updateBTMIDIDeviceName(const char* name);
extern void updateBTMIDIInfo(int wpm, bool fromMidi, const char* keyerName);
extern void updateBTMIDIKeyIndicator(bool keying);
extern void cleanupBTMIDIScreen();

// Track previous connection state for UI updates
static BLEConnectionState lastBTMIDIState = BLE_STATE_OFF;

const char* getBTMIDIKeyerProgramName() {
  switch (btMIDI.midiKeyerProgram) {
    case MIDI_KEYER_PASSTHROUGH: return "Passthrough";
    case MIDI_KEYER_STRAIGHT:    return "Straight";
    case MIDI_KEYER_BUG:         return "Bug";
    case MIDI_KEYER_IAMBIC_A:    return "Iambic A";
    case MIDI_KEYER_IAMBIC_B:    return "Iambic B";
    default:                     return "Unknown";
  }
}

// Push current speed + keyer program to the LVGL screen
static void refreshBTMIDIInfoDisplay() {
  int wpm = (btMIDI.midiDitDuration > 0) ? (1200 / btMIDI.midiDitDuration) : cwSpeed;
  updateBTMIDIInfo(wpm, btMIDI.midiDitDuration > 0, getBTMIDIKeyerProgramName());
}

// Convert MIDI note to frequency (equal temperament, A4=440Hz)
int midiNoteToFrequency(int note) {
  // f = 440 * 2^((n-69)/12)
  float freq = 440.0 * pow(2.0, (note - 69) / 12.0);
  return (int)freq;
}

// Get current dit duration (MIDI override or device setting)
int getDitDuration() {
  if (btMIDI.midiDitDuration > 0) {
    return btMIDI.midiDitDuration;
  }
  return DIT_DURATION(cwSpeed);
}

// MIDI characteristic callback for receiving data
class MIDICharacteristicCallbacks : public NimBLECharacteristicCallbacks {
  void onWrite(NimBLECharacteristic* pCharacteristic) override {
    std::string value = pCharacteristic->getValue();
    Serial.print("MIDI onWrite: ");
    Serial.print(value.length());
    Serial.println(" bytes");
    if (value.length() > 0) {
      onMIDIReceived((uint8_t*)value.data(), value.length());
    }
  }

  void onRead(NimBLECharacteristic* pCharacteristic) override {
    Serial.println("MIDI onRead");
  }

  // Note: onNotify() and onStatus() removed - not in NimBLECharacteristicCallbacks base class
};

// Process received MIDI data
// BLE MIDI packet format: [Header][Timestamp][Status][Data...][Timestamp][Status][Data...]...
// Header byte: 1ttttttt (bit 7 always 1, bits 0-5 = timestamp high)
// Timestamp byte: 1ttttttt (bit 7 always 1, bits 0-6 = timestamp low)
// MIDI messages follow timestamps
void onMIDIReceived(uint8_t* data, size_t length) {
  if (length < 3) return;  // Minimum: header + timestamp + 1 MIDI byte

  Serial.print("BLE MIDI RX: ");
  for (size_t i = 0; i < length; i++) {
    Serial.print(data[i], HEX);
    Serial.print(" ");
  }
  Serial.println();

  // First byte is header (must have bit 7 set)
  if (!(data[0] & 0x80)) return;

  size_t pos = 1;  // Skip header byte
  uint8_t runningStatus = 0;

  while (pos < length) {
    // Check for timestamp byte (bit 7 set, but not a status byte pattern we care about)
    if ((data[pos] & 0x80) && pos + 1 < length) {
      // This could be a timestamp or a status byte
      uint8_t byte = data[pos];

      // Check if next byte looks like MIDI data (bit 7 clear) - then this is likely timestamp
      if (!(data[pos + 1] & 0x80)) {
        // Likely a timestamp followed by data using running status
        pos++;
        continue;
      }

      // Check if this is a MIDI status byte (0x80-0xEF for channel messages)
      uint8_t msgType = byte & 0xF0;
      if (msgType >= 0x80 && msgType <= 0xE0) {
        runningStatus = byte;
        pos++;

        // Parse MIDI message based on status
        if (msgType == MIDI_NOTE_ON && pos + 1 < length) {
          uint8_t note = data[pos] & 0x7F;
          uint8_t velocity = data[pos + 1] & 0x7F;
          pos += 2;

          if (velocity > 0) {
            int freq = midiNoteToFrequency(note);
            Serial.print("MIDI Note On: note=");
            Serial.print(note);
            Serial.print(" freq=");
            Serial.println(freq);
            startTone(freq);
          } else {
            Serial.println("MIDI Note Off (velocity 0)");
            stopTone();
          }

        } else if (msgType == MIDI_NOTE_OFF && pos + 1 < length) {
          pos += 2;  // Skip note and velocity
          Serial.println("MIDI Note Off");
          stopTone();

        } else if (msgType == MIDI_CONTROL_CHANGE && pos + 1 < length) {
          uint8_t cc = data[pos] & 0x7F;
          uint8_t value = data[pos + 1] & 0x7F;
          pos += 2;

          if (cc == MIDI_CC_DIT_DURATION) {
            btMIDI.midiDitDuration = value * 2;
            Serial.print("MIDI CC1 Dit Duration: ");
            Serial.print(btMIDI.midiDitDuration);
            Serial.println("ms");
          } else if (cc == MIDI_CC_SIDETONE_NOTE) {
            btMIDI.midiSidetoneNote = value;
            Serial.print("MIDI CC2 Sidetone Note: ");
            Serial.println(value);
          }

        } else if (msgType == MIDI_PROGRAM_CHANGE && pos < length) {
          uint8_t program = data[pos] & 0x7F;
          pos++;
          btMIDI.midiKeyerProgram = program;
          // Reinitialize keyer for new program
          btMidiInitKeyer();
          Serial.print("MIDI Program Change: ");
          Serial.println(program);

        } else {
          // Unknown message type, skip
          pos++;
        }
      } else {
        // Timestamp byte, skip it
        pos++;
      }
    } else {
      // Data byte or unknown, skip
      pos++;
    }
  }
}

// Send MIDI Note On
void sendMIDINoteOn(uint8_t note, uint8_t velocity) {
  if (!btMIDI.active || btMIDI.midiCharacteristic == nullptr) return;
  if (!isBLEConnected()) return;

  // BLE MIDI packet: [Header, Timestamp High, Status, Note, Velocity]
  uint8_t timestamp = (millis() & 0x1FFF) >> 7;  // 6-bit timestamp high
  uint8_t packet[5] = {
    (uint8_t)(0x80 | timestamp),    // Header with timestamp
    (uint8_t)(0x80 | (millis() & 0x7F)),  // Timestamp low
    (uint8_t)(MIDI_NOTE_ON | 0),    // Note On, channel 0
    note,
    velocity
  };

  btMIDI.midiCharacteristic->setValue(packet, sizeof(packet));
  btMIDI.midiCharacteristic->notify();

  Serial.print("Sent MIDI Note On: ");
  Serial.println(note);
}

// Send MIDI Note Off
void sendMIDINoteOff(uint8_t note) {
  if (!btMIDI.active || btMIDI.midiCharacteristic == nullptr) return;
  if (!isBLEConnected()) return;

  uint8_t timestamp = (millis() & 0x1FFF) >> 7;
  uint8_t packet[5] = {
    (uint8_t)(0x80 | timestamp),
    (uint8_t)(0x80 | (millis() & 0x7F)),
    (uint8_t)(MIDI_NOTE_OFF | 0),
    note,
    0x40  // Release velocity
  };

  btMIDI.midiCharacteristic->setValue(packet, sizeof(packet));
  btMIDI.midiCharacteristic->notify();

  Serial.print("Sent MIDI Note Off: ");
  Serial.println(note);
}

// Start BT MIDI mode
void startBTMIDI(LGFX& display) {
  Serial.println("Starting BT MIDI mode");

  // Reset state
  btMIDI.active = true;
  btMIDI.isKeying = false;
  btMIDI.lastDitPressed = false;
  btMIDI.lastDahPressed = false;
  btMIDI.midiDitDuration = 0;  // Use device settings by default
  btMIDI.midiSidetoneNote = 69;
  btMIDI.midiKeyerProgram = MIDI_KEYER_IAMBIC_B;
  btMIDI.lastUpdateTime = millis();

  // Initialize unified keyer (will be updated when MIDI keyer program changes)
  btMIDIDitPressed = false;
  btMIDIDahPressed = false;
  btMIDIKeyer = nullptr;  // Initialized in btMidiInitKeyer() based on program
  lastBTMIDIState = BLE_STATE_OFF;  // Reset state tracking

  // Release the BLE keyboard host (central role) before bringing up the MIDI
  // server — they can't share the NimBLE stack lifecycle, and deinitBLECore()
  // on exit would otherwise free the host's client out from under it
  if (bleKBHost.state != BLEKB_STATE_IDLE) {
    deinitBLEKeyboardHost();
  }

  // Initialize BLE core if not already done
  initBLECore();
  bleCore.activeMode = BLE_MODE_MIDI;

  // Create MIDI service
  btMIDI.midiService = bleCore.pServer->createService(MIDI_SERVICE_UUID);
  Serial.print("BLE MIDI: Service UUID = ");
  Serial.println(MIDI_SERVICE_UUID);

  // Create MIDI characteristic with standard BLE MIDI properties
  btMIDI.midiCharacteristic = btMIDI.midiService->createCharacteristic(
    MIDI_CHARACTERISTIC_UUID,
    NIMBLE_PROPERTY::READ |
    NIMBLE_PROPERTY::WRITE |
    NIMBLE_PROPERTY::NOTIFY |
    NIMBLE_PROPERTY::WRITE_NR
  );
  Serial.print("BLE MIDI: Characteristic UUID = ");
  Serial.println(MIDI_CHARACTERISTIC_UUID);

  // Set callback for receiving MIDI
  btMIDI.midiCharacteristic->setCallbacks(new MIDICharacteristicCallbacks());

  // Set security for bonding (required for some BLE MIDI clients)
  NimBLEDevice::setSecurityAuth(true, false, true);  // bonding, MITM, SC

  // Start service
  btMIDI.midiService->start();
  Serial.println("BLE MIDI: Service started");

  // Set up advertising
  NimBLEAdvertising* advertising = NimBLEDevice::getAdvertising();
  advertising->addServiceUUID(btMIDI.midiService->getUUID());
  advertising->setAppearance(0x00);  // Generic appearance

  // Start advertising
  startBLEAdvertising("MIDI");

  // Initialize LVGL UI with device name, status, and current settings
  updateBTMIDIDeviceName(getBLEDeviceName().c_str());
  updateBTMIDIStatus("Advertising...", false);
  refreshBTMIDIInfoDisplay();
  updateBTMIDIKeyIndicator(false);
}

// Stop BT MIDI mode
void stopBTMIDI() {
  Serial.println("Stopping BT MIDI mode");

  // Send note off if keying
  if (btMIDI.active && btMIDI.isKeying) {
    sendMIDINoteOff(MIDI_NOTE_STRAIGHT);
    btMIDI.isKeying = false;
  }

  // Stop any local sidetone
  stopTone();

  btMIDI.active = false;
  btMIDI.midiService = nullptr;
  btMIDI.midiCharacteristic = nullptr;

  // Clean up LVGL widget pointers
  cleanupBTMIDIScreen();

  // Deinit BLE
  deinitBLECore();

  // Hand the radio back to the keyboard host so auto-reconnect resumes
  if (bleKBHost.pairedDevice.valid && bleKBHost.autoReconnect) {
    initBLEKeyboardHost();
  }
}

// Draw BT MIDI UI
void drawBTMIDIUI(LGFX& display) {
  // Clear screen (preserve header)
  display.fillRect(0, 42, SCREEN_WIDTH, SCREEN_HEIGHT - 42, COLOR_BACKGROUND);

  // Status card
  int cardX = 20;
  int cardY = 55;
  int cardW = SCREEN_WIDTH - 40;
  int cardH = 100;

  display.fillRoundRect(cardX, cardY, cardW, cardH, 12, 0x1082);
  display.drawRoundRect(cardX, cardY, cardW, cardH, 12, 0x34BF);

  // Connection status
  display.setFont(&FreeSansBold12pt7b);
  display.setTextSize(1);

  int yPos = cardY + 30;
  display.setCursor(cardX + 15, yPos);

  if (isBLEConnected()) {
    display.setTextColor(ST77XX_GREEN);
    display.print("Connected");
  } else if (isBLEAdvertising()) {
    display.setTextColor(ST77XX_YELLOW);
    display.print("Advertising...");
  } else {
    display.setTextColor(ST77XX_RED);
    display.print("Disconnected");
  }

  // Device name
  display.setFont(nullptr);
  display.setTextSize(2);
  display.setTextColor(ST77XX_CYAN);
  yPos += 35;
  display.setCursor(cardX + 15, yPos);
  display.print(getBLEDeviceName());

  // Settings card
  cardY = 170;
  cardH = 90;
  display.fillRoundRect(cardX, cardY, cardW, cardH, 12, 0x1082);
  display.drawRoundRect(cardX, cardY, cardW, cardH, 12, 0x34BF);

  display.setTextSize(1);
  display.setTextColor(0x7BEF);
  yPos = cardY + 12;
  display.setCursor(cardX + 15, yPos);
  display.print("Current Settings:");

  display.setTextSize(2);
  display.setTextColor(ST77XX_WHITE);

  // Speed
  yPos += 20;
  display.setCursor(cardX + 15, yPos);
  display.print("Speed: ");
  if (btMIDI.midiDitDuration > 0) {
    int wpm = 1200 / btMIDI.midiDitDuration;
    display.print(wpm);
    display.print(" WPM (MIDI)");
  } else {
    display.print(cwSpeed);
    display.print(" WPM");
  }

  // Keyer type
  yPos += 22;
  display.setCursor(cardX + 15, yPos);
  display.print("Keyer: ");
  switch (btMIDI.midiKeyerProgram) {
    case MIDI_KEYER_PASSTHROUGH: display.print("Passthrough"); break;
    case MIDI_KEYER_STRAIGHT: display.print("Straight"); break;
    case MIDI_KEYER_BUG: display.print("Bug"); break;
    case MIDI_KEYER_IAMBIC_A: display.print("Iambic A"); break;
    case MIDI_KEYER_IAMBIC_B: display.print("Iambic B"); break;
    default: display.print("Unknown"); break;
  }

  // Instructions
  display.setTextSize(1);
  display.setTextColor(ST77XX_YELLOW);
  display.setCursor(cardX + 15, SCREEN_HEIGHT - 50);
  display.print("macOS: Works with Web MIDI natively");
  display.setCursor(cardX + 15, SCREEN_HEIGHT - 35);
  display.print("Windows: Needs MIDIberry or similar app");

  display.setFont(nullptr);
}

// Handle BT MIDI keyboard input
int handleBTMIDIInput(char key, LGFX& display) {
  if (key == KEY_ESC) {
    stopBTMIDI();
    return -1;  // Exit mode
  }

  return 0;  // Normal input
}

// Keyer callback for unified keyer - sends MIDI notes
void btMidiKeyerCallback(bool txOn, int element) {
  if (txOn) {
    sendMIDINoteOn(MIDI_NOTE_STRAIGHT, 127);
    startTone(TONE_SIDETONE);
    btMIDI.isKeying = true;
  } else {
    sendMIDINoteOff(MIDI_NOTE_STRAIGHT);
    stopTone();
    btMIDI.isKeying = false;
  }
}

// Initialize unified keyer based on MIDI keyer program
void btMidiInitKeyer() {
  btMIDIDitPressed = false;
  btMIDIDahPressed = false;

  // Map MIDI keyer program to unified keyer type
  int keyerType;
  switch (btMIDI.midiKeyerProgram) {
    case MIDI_KEYER_STRAIGHT:
      keyerType = KEY_STRAIGHT;
      break;
    case MIDI_KEYER_IAMBIC_A:
      keyerType = KEY_IAMBIC_A;
      break;
    case MIDI_KEYER_IAMBIC_B:
      keyerType = KEY_IAMBIC_B;
      break;
    default:
      // Passthrough and Bug don't use the keyer
      btMIDIKeyer = nullptr;
      return;
  }

  btMIDIKeyer = getKeyer(keyerType);
  btMIDIKeyer->reset();
  btMIDIKeyer->setDitDuration(getDitDuration());
  btMIDIKeyer->setTxCallback(btMidiKeyerCallback);
}

// Passthrough handler (raw dit/dah)
void btMidiPassthroughHandler() {
  // Get paddle state from centralized handler (includes debounce)
  bool ditPressed, dahPressed;
  getPaddleState(&ditPressed, &dahPressed);

  // Send dit state changes
  if (ditPressed != btMIDI.lastDitPressed) {
    if (ditPressed) {
      sendMIDINoteOn(MIDI_NOTE_DIT, 127);
      startTone(TONE_SIDETONE);
    } else {
      sendMIDINoteOff(MIDI_NOTE_DIT);
      if (!dahPressed) stopTone();
    }
    btMIDI.lastDitPressed = ditPressed;
  }

  // Send dah state changes
  if (dahPressed != btMIDI.lastDahPressed) {
    if (dahPressed) {
      sendMIDINoteOn(MIDI_NOTE_DAH, 127);
      startTone(TONE_SIDETONE);
    } else {
      sendMIDINoteOff(MIDI_NOTE_DAH);
      if (!ditPressed) stopTone();
    }
    btMIDI.lastDahPressed = dahPressed;
  }

  // Keep audio buffer filled while any paddle pressed
  if (ditPressed || dahPressed) {
    continueTone(TONE_SIDETONE);
  }
}

// Keyer handler (uses unified keyer module)
void btMidiKeyerHandler() {
  // Initialize keyer on first call if needed
  if (!btMIDIKeyer) {
    btMidiInitKeyer();
  }
  if (!btMIDIKeyer) return;  // Still null = passthrough mode

  // Get paddle state from centralized handler (includes debounce)
  bool ditPressed, dahPressed;
  getPaddleState(&ditPressed, &dahPressed);

  unsigned long currentTime = millis();

  // Feed paddle state to unified keyer
  if (ditPressed != btMIDIDitPressed) {
    btMIDIKeyer->key(PADDLE_DIT, ditPressed);
    btMIDIDitPressed = ditPressed;
  }
  if (dahPressed != btMIDIDahPressed) {
    btMIDIKeyer->key(PADDLE_DAH, dahPressed);
    btMIDIDahPressed = dahPressed;
  }

  // Tick the keyer state machine
  btMIDIKeyer->tick(currentTime);

  // Keep tone playing if keyer is active
  if (btMIDIKeyer->isTxActive()) {
    continueTone(TONE_SIDETONE);
  }

  btMIDI.lastDitPressed = ditPressed;
  btMIDI.lastDahPressed = dahPressed;
}

// Update BT MIDI (called from main loop)
void updateBTMIDI() {
  if (!btMIDI.active) return;

  // Check for connection state changes and update LVGL UI
  // (UI updates must happen here in the main loop, not in BLE task callbacks)
  if (bleCore.connectionState != lastBTMIDIState) {
    lastBTMIDIState = bleCore.connectionState;
    switch (lastBTMIDIState) {
      case BLE_STATE_CONNECTED:   updateBTMIDIStatus("Connected", true); break;
      case BLE_STATE_ADVERTISING: updateBTMIDIStatus("Advertising...", false); break;
      case BLE_STATE_ERROR:       updateBTMIDIStatus("Error", false); break;
      default:                    updateBTMIDIStatus("Off", false); break;
    }
  }

  // The host can change keyer program (Program Change) and speed (CC1) at any
  // time from the BLE task — pick up those changes here and refresh the UI
  static int lastShownProgram = -1;
  static int lastShownDitDuration = -1;
  if (btMIDI.midiKeyerProgram != lastShownProgram ||
      btMIDI.midiDitDuration != lastShownDitDuration) {
    lastShownProgram = btMIDI.midiKeyerProgram;
    lastShownDitDuration = btMIDI.midiDitDuration;
    refreshBTMIDIInfoDisplay();
  }

  // Route to appropriate handler based on keyer program
  if (btMIDI.midiKeyerProgram == MIDI_KEYER_PASSTHROUGH) {
    btMidiPassthroughHandler();
  } else {
    btMidiKeyerHandler();
  }

  // Keep audio buffer filled while keying
  if (btMIDI.isKeying) {
    continueTone(TONE_SIDETONE);
  }

  // Update the keying LED on state change
  static bool lastShownKeying = false;
  bool keyingNow = btMIDI.isKeying || btMIDI.lastDitPressed || btMIDI.lastDahPressed;
  if (keyingNow != lastShownKeying) {
    lastShownKeying = keyingNow;
    updateBTMIDIKeyIndicator(keyingNow);
  }

  btMIDI.lastUpdateTime = millis();
}

#endif // BLE_MIDI_H
