Vail-CW/vail-summit/src/audio/i2s_audio.h

/*
 * I2S Audio Library for MAX98357A Class-D Amplifier
 * Replaces PWM buzzer with high-quality audio output
 * Includes software volume control (0-100%)
 */

#ifndef I2S_AUDIO_H
#define I2S_AUDIO_H

#include <driver/i2s.h>
#include <driver/gpio.h>
#include <math.h>
#include <Preferences.h>
#include "../core/config.h"
#include "../core/deferred_save.h"

// I2S port number
#define I2S_NUM I2S_NUM_0

// Base amplitude for audio output (max 32767 for 16-bit). This is the digital
// ceiling at 100% volume; the perceptual curve (getVolumeScale) scales down
// from here. NOTE: the earlier "distortion at any level" was a hardware fault
// (the MAX98357A LRC/word-select pin was unsoldered, so I2S framing was broken)
// - not amplitude. With proper I2S, this moderate level is clean.
#define I2S_BASE_AMPLITUDE 8000

// DMA ring depth. 16 buffers x 64 frames at 22050Hz gives roughly 46ms of
// buffered audio to ride out a Core-1 flash-cache stall, versus ~23ms at the
// previous depth of 8. This does not add keying latency: stopTone() calls
// i2s_zero_dma_buffer() on every tone stop (see below), so a deeper ring never
// plays back stale samples after a key-up - depth only matters while a tone
// is actively feeding, which is exactly the window a stall can hit.
#define I2S_DMA_BUF_COUNT 16

// Forward declarations
void IRAM_ATTR continueTone(int frequency);
static void initSineLUT();

// ============================================
// Audio performance instrumentation
// ============================================
// Profiling aid for the Core-0 audio hot path, added to verify the IRAM /
// DMA-depth changes below actually keep the sidetone fed while Core 1 is
// hammering the flash cache with display work. Set to 0 to compile it out
// completely. Mirrors the shape of DISPLAY_PERF_INSTRUMENT in lv_init.h.
//
// Reported once per second, from the audio task itself:
//   iter/s     audio task loop iterations per second
//   worst      the single slowest loop iteration (processAudioRequests +
//              processMorsePlayback + samplePaddleInput), in ms
//   over5ms    count of iterations that took longer than 5ms - these are the
//              cache-contention stalls we're chasing
//   write_max  the single slowest i2s_write() call across all call sites, in ms
//
// The report itself uses Serial.printf (flash-resident), so it is only ever
// called once per second, from OUTSIDE the measured region - never from the
// per-iteration hot path.
#define AUDIO_PERF_INSTRUMENT 0

#if AUDIO_PERF_INSTRUMENT
static uint32_t aperf_iterations     = 0;
static uint32_t aperf_worst_loop_us  = 0;
static uint32_t aperf_over5ms_count  = 0;
static uint32_t aperf_worst_write_us = 0;
static uint32_t aperf_window_start   = 0;

// Called once per second from the audio task loop, after vTaskDelay(1) so
// this Serial.printf never runs inside the measured region.
void reportAudioPerf() {
    uint32_t now = millis();
    if (aperf_window_start == 0) { aperf_window_start = now; return; }
    uint32_t elapsed_ms = now - aperf_window_start;
    if (elapsed_ms < 1000) return;

    Serial.printf("[AudioPerf] iter/s=%lu worst=%.2fms over5ms=%lu write_max=%.2fms\n",
                  (unsigned long)(aperf_iterations * 1000UL / elapsed_ms),
                  aperf_worst_loop_us / 1000.0f,
                  (unsigned long)aperf_over5ms_count,
                  aperf_worst_write_us / 1000.0f);

    aperf_iterations = 0;
    aperf_worst_loop_us = 0;
    aperf_over5ms_count = 0;
    aperf_worst_write_us = 0;
    aperf_window_start = now;
}
#else
inline void reportAudioPerf() {}
#endif

// Boot preset options
enum BootPreset {
    BOOT_NORMAL = 0,      // Boot at last saved volume
    BOOT_LOW_VOLUME = 1,  // Boot at 10% (legacy quiet boot)
    BOOT_HEADPHONES = 2,  // Boot at headphones preset
    BOOT_SPEAKER = 3      // Boot at speaker preset
};

// Global audio state
static bool i2s_initialized = false;
static bool tone_playing = false;
static unsigned long tone_start_time = 0;
static unsigned long tone_duration = 0;
static float phase = 0.0;  // Phase accumulator for continuous tone
static int current_frequency = 0;
static int audio_volume = DEFAULT_VOLUME;  // Volume 0-100%
static bool quiet_boot_enabled = false;    // Boot at low volume (10%) - legacy, migrated to bootPreset
static int headphones_preset = 25;         // Headphones preset volume
static int speaker_preset = 75;            // Speaker preset volume
static int boot_preset = BOOT_NORMAL;      // Boot volume option
static Preferences volumePrefs;

/*
 * Load volume from preferences
 * Also loads presets and boot option, with migration from legacy quietboot
 */
void loadVolume() {
  volumePrefs.begin("audio", false);

  // Load main volume
  audio_volume = volumePrefs.getInt("volume", DEFAULT_VOLUME);
  if (audio_volume < VOLUME_MIN || audio_volume > VOLUME_MAX) {
    audio_volume = DEFAULT_VOLUME;
  }

  // Load presets
  headphones_preset = volumePrefs.getInt("presetHP", 25);
  speaker_preset = volumePrefs.getInt("presetSpk", 75);

  // Migration: check for legacy quietboot setting
  bool hasBootPreset = volumePrefs.isKey("bootPreset");
  quiet_boot_enabled = volumePrefs.getBool("quietboot", false);

  if (!hasBootPreset) {
    // First run after update - migrate from quietboot
    if (quiet_boot_enabled) {
      boot_preset = BOOT_LOW_VOLUME;
      Serial.println("Migrated quietboot=true to BOOT_LOW_VOLUME");
    } else {
      boot_preset = BOOT_NORMAL;
    }
    volumePrefs.putInt("bootPreset", boot_preset);
  } else {
    boot_preset = volumePrefs.getInt("bootPreset", BOOT_NORMAL);
  }

  volumePrefs.end();

  Serial.printf("Loaded volume: %d%%\n", audio_volume);
  Serial.printf("Headphones preset: %d%%, Speaker preset: %d%%\n", headphones_preset, speaker_preset);
  Serial.printf("Boot preset: %d\n", boot_preset);

  // Apply boot preset override
  switch (boot_preset) {
    case BOOT_LOW_VOLUME:
      audio_volume = 10;
      Serial.println("Boot preset: Low volume (10%)");
      break;
    case BOOT_HEADPHONES:
      audio_volume = headphones_preset;
      Serial.printf("Boot preset: Headphones (%d%%)\n", audio_volume);
      break;
    case BOOT_SPEAKER:
      audio_volume = speaker_preset;
      Serial.printf("Boot preset: Speaker (%d%%)\n", audio_volume);
      break;
    case BOOT_NORMAL:
    default:
      Serial.println("Boot preset: Normal (saved volume)");
      break;
  }
}

/*
 * Save volume to preferences
 */
void saveVolume() {
  volumePrefs.begin("audio", false);
  volumePrefs.putInt("volume", audio_volume);
  volumePrefs.end();
  Serial.printf("Saved volume: %d%%\n", audio_volume);
}

/*
 * Set volume (0-100%)
 */
void setVolume(int vol) {
  audio_volume = constrain(vol, VOLUME_MIN, VOLUME_MAX);
  // Deferred: an NVS commit per slider tick crunches the live beep
  markDeferredSave(saveVolume);
}

/*
 * Get current volume
 */
int getVolume() {
  return audio_volume;
}

/*
 * Load quiet boot setting from preferences
 */
void loadQuietBoot() {
  volumePrefs.begin("audio", false);
  quiet_boot_enabled = volumePrefs.getBool("quietboot", false);
  volumePrefs.end();
  Serial.printf("Loaded quiet boot: %s\n", quiet_boot_enabled ? "enabled" : "disabled");
}

/*
 * Save quiet boot setting to preferences
 */
void saveQuietBoot(bool enabled) {
  quiet_boot_enabled = enabled;
  volumePrefs.begin("audio", false);
  volumePrefs.putBool("quietboot", enabled);
  volumePrefs.end();
  Serial.printf("Saved quiet boot: %s\n", enabled ? "enabled" : "disabled");
}

/*
 * Get quiet boot setting
 */
bool getQuietBootEnabled() {
  return quiet_boot_enabled;
}

/*
 * Set quiet boot setting
 */
void setQuietBootEnabled(bool enabled) {
  saveQuietBoot(enabled);
}

/*
 * Get headphones preset volume
 */
int getHeadphonesPreset() {
  return headphones_preset;
}

/*
 * Set headphones preset volume
 */
void setHeadphonesPreset(int vol) {
  headphones_preset = constrain(vol, VOLUME_MIN, VOLUME_MAX);
  volumePrefs.begin("audio", false);
  volumePrefs.putInt("presetHP", headphones_preset);
  volumePrefs.end();
  Serial.printf("Saved headphones preset: %d%%\n", headphones_preset);
}

/*
 * Get speaker preset volume
 */
int getSpeakerPreset() {
  return speaker_preset;
}

/*
 * Set speaker preset volume
 */
void setSpeakerPreset(int vol) {
  speaker_preset = constrain(vol, VOLUME_MIN, VOLUME_MAX);
  volumePrefs.begin("audio", false);
  volumePrefs.putInt("presetSpk", speaker_preset);
  volumePrefs.end();
  Serial.printf("Saved speaker preset: %d%%\n", speaker_preset);
}

/*
 * Get boot preset option
 */
int getBootPreset() {
  return boot_preset;
}

/*
 * Set boot preset option
 */
void setBootPreset(int preset) {
  boot_preset = preset;
  volumePrefs.begin("audio", false);
  volumePrefs.putInt("bootPreset", boot_preset);
  volumePrefs.end();
  Serial.printf("Saved boot preset: %d\n", boot_preset);
}
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
